kevinisabelle/raspigamecontroller/rust/src/constants.rs

pub const AGENT_PATH: &str = "/com/kevinisabelle/gamepadki/agent";
pub const ADVERT_PATH: &str = "/org/bluez/gamepadki/advertisement0";
pub const DEVICE_PATH: &str = "/org/bluez/hci0";
pub const APP_PATH: &str = "/com/kevinisabelle/gamepadki/app0";
pub const BLUEZ_SERVICE: &str = "org.bluez";
pub const BLUEZ_SERVICE_PATH: &str = "/org/bluez";
pub const ADAPTER_PATH: &str = "/org/bluez/hci0"; // adjust if needed
pub const AGENT_MANAGER_IFACE: &str = "org.bluez.AgentManager1";
pub const DBUS_PROPERTIES_IFACE: &str = "org.freedesktop.DBus.Properties";
pub const ADAPTER_IFACE: &str = "org.bluez.Adapter1";
pub const LE_ADVERTISING_MANAGER_IFACE: &str = "org.bluez.LEAdvertisingManager1";
pub const GATT_DESCRIPTOR_IFACE: &str = "org.bluez.GattDescriptor1";
pub const GATT_CHARACTERISTIC_IFACE: &str = "org.bluez.GattCharacteristic1";
pub const GATT_SERVICE_IFACE: &str = "org.bluez.GattService1";
pub const GATT_APPLICATION_IFACE: &str = "org.bluez.GattApplication1";
pub const ADV_APPEARANCE_GAMEPAD: u16 = 0x03c4;
pub const GATT_SERVICE_HID_UUID: &str = "00001812-0000-1000-8000-00805f9b34fb";
pub const GATT_REPORT_MAP_UUID: &str = "00002A4B-0000-1000-8000-00805f9b34fb";
pub const GATT_REPORT_UUID: &str = "00002A4D-0000-1000-8000-00805f9b34fb";
pub const GATT_HID_INFORMATION_UUID: &str = "00002A4A-0000-1000-8000-00805f9b34fb";
pub const GATT_PROTOCOL_MODE_UUID: &str = "00002A4E-0000-1000-8000-00805f9b34fb";
pub const GATT_HID_CONTROL_POINT_UUID: &str = "00002A4C-0000-1000-8000-00805f9b34fb";
pub const DEVICE_INFORMATION_SERVICE_UUID: &str = "0000180a-0000-1000-8000-00805f9b34fb";
pub const BATTERY_SERVICE_UUID: &str = "0000180f-0000-1000-8000-00805f9b34fb";
pub const GATT_DESC_REPORT_REFERENCE_UUID: &str = "00002908-0000-1000-8000-00805f9b34fb";
pub const GATT_DESC_CLIENT_DESCRIPTOR_UUID: &str = "00002902-0000-1000-8000-00805f9b34fb";
pub const SERIAL_NUMBER_CHARACTERISTIC_UUID: &str = "00002A25-0000-1000-8000-00805f9b34fb";
