kevinisabelle/raspigamecontroller/python/Constants.py

BLUEZ_AGENT_IFACE = "org.bluez.Agent1"
BLUEZ_LEADVERTISEMENT_IFACE = "org.bluez.LEAdvertisement1"
BLUEZ_LEADVERTISEMENT_MANAGER_IFACE = "org.bluez.LEAdvertisingManager1"
BLUEZ_GATT_CHARACTERISTIC_IFACE = "org.bluez.GattCharacteristic1"
BLUEZ_GATT_DESCRIPTOR_IFACE = "org.bluez.GattDescriptor1"
BLUEZ_GATT_SERVICE_IFACE = "org.bluez.GattService1"
BLUEZ_GATT_MANAGER_IFACE = "org.bluez.GattManager1"
DBUS_PROPERTIES_IFACE = "org.freedesktop.DBus.Properties"
DBUS_OM_IFACE = "org.freedesktop.DBus.ObjectManager"

BLUEZ_SERVICE = "org.bluez"
ADV_APPEARANCE_GAMEPAD = 0x03C4

GATT_SERVICE_HID_UUID = "00001812-0000-1000-8000-00805f9b34fb"
GATT_REPORT_MAP_UUID = "00002A4B-0000-1000-8000-00805f9b34fb"
GATT_REPORT_UUID = "00002A4D-0000-1000-8000-00805f9b34fb"
GATT_HID_INFORMATION_UUID = "00002A4A-0000-1000-8000-00805f9b34fb"
GATT_PROTOCOL_MODE_UUID = "00002A4E-0000-1000-8000-00805f9b34fb"
GATT_HID_CONTROL_POINT_UUID = "00002A4C-0000-1000-8000-00805f9b34fb"
DEVICE_INFORMATION_SERVICE_UUID = "0000180a-0000-1000-8000-00805f9b34fb"
BATTERY_SERVICE_UUID = "0000180f-0000-1000-8000-00805f9b34fb"

GATT_DESC_REPORT_REFERENCE_UUID = "00002908-0000-1000-8000-00805f9b34fb"
GATT_DESC_CLIENT_DESCRIPTOR_UUID = "00002902-0000-1000-8000-00805f9b34fb"

SERIAL_NUMBER_CHARACTERISTIC_UUID = "00002A25-0000-1000-8000-00805f9b34fb"

AGENT_PATH = "/com/kevinisabelle/gamepadki/agent"
SERVICE_PATH = "/org/bluez/gamepadki/service"
ADVERTISEMENT_PATH = "/org/bluez/gamepadki/advertisement"
ADAPTER_PATH = "/org/bluez/hci0"
BLUEZ_SERVICE_PATH = "/org/bluez"
